markus-k/led-controller-hardware/images/IMG_4800.jpg

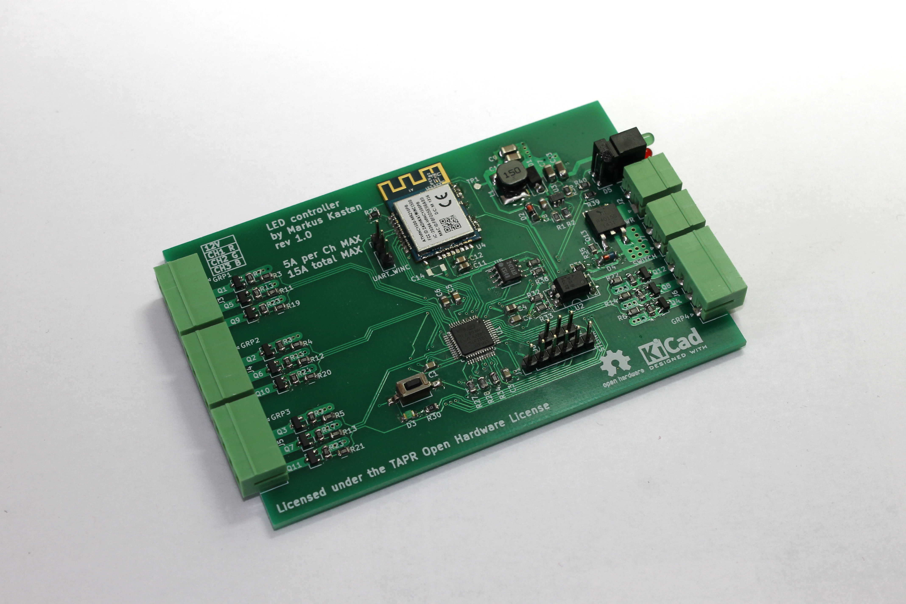
images/IMG_4800.jpg
